systronix/ultim8x64/kicad/ultim8x64_pdf/ultim8x64.pdf

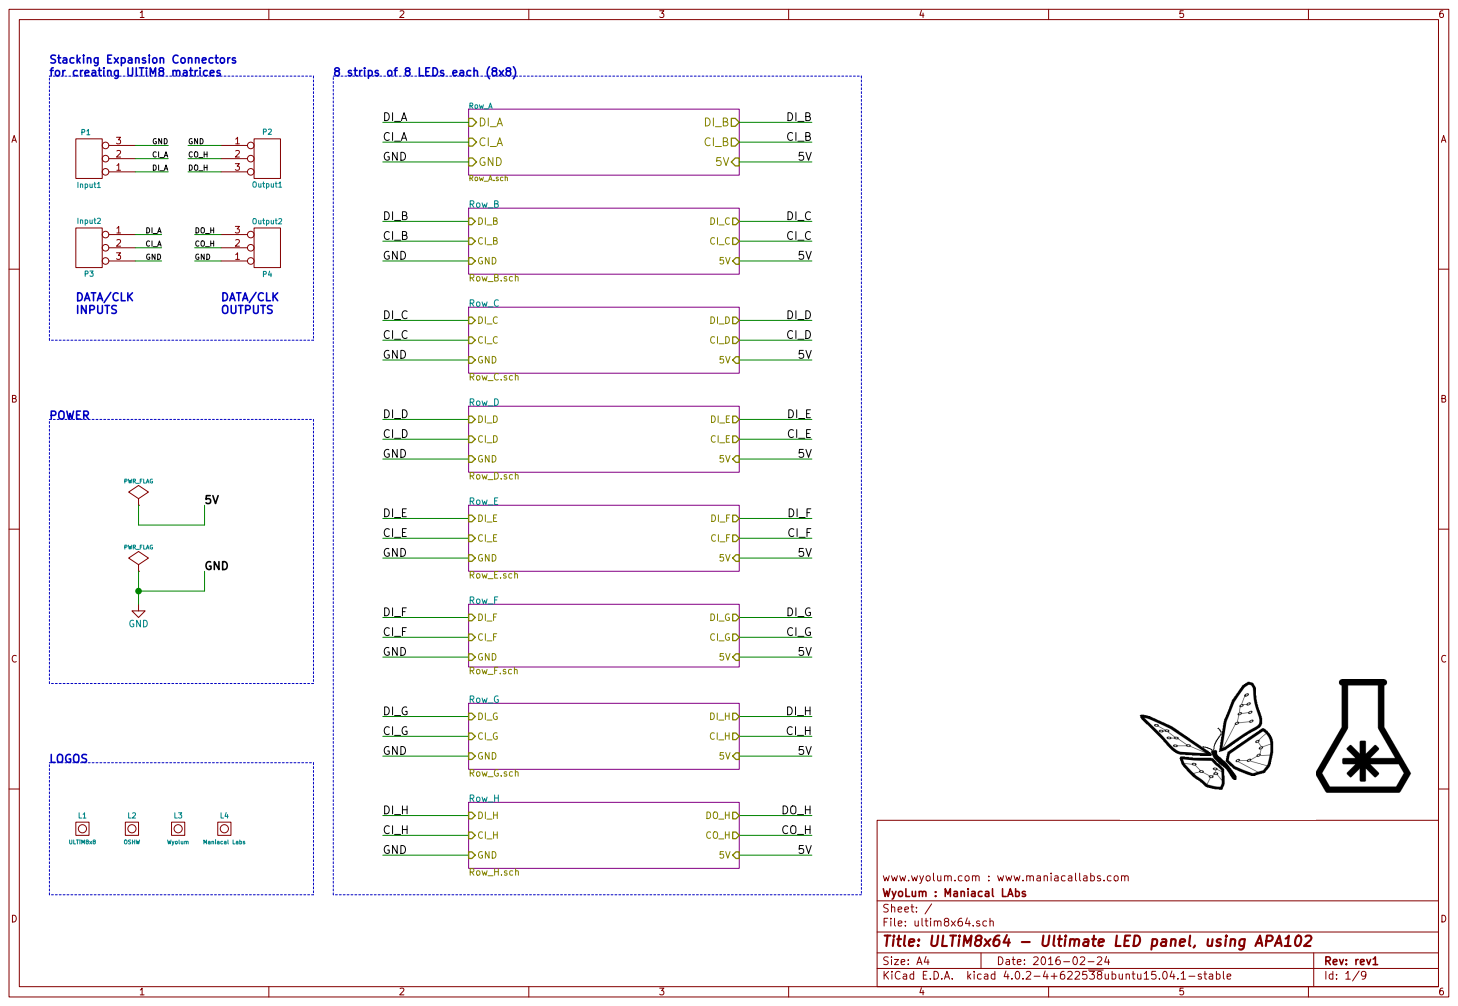
[picture p13: page 1]

8 strips of 8 LEDs each (8x8)

www.wyolum.com : www.maniacallabs.com
File: ultim8x64.sch Sheet: / WyoLum : Maniacal LAbs

Id: 1/9 Title: ULTiM8x64 - Ultimate LED panel, using APA102

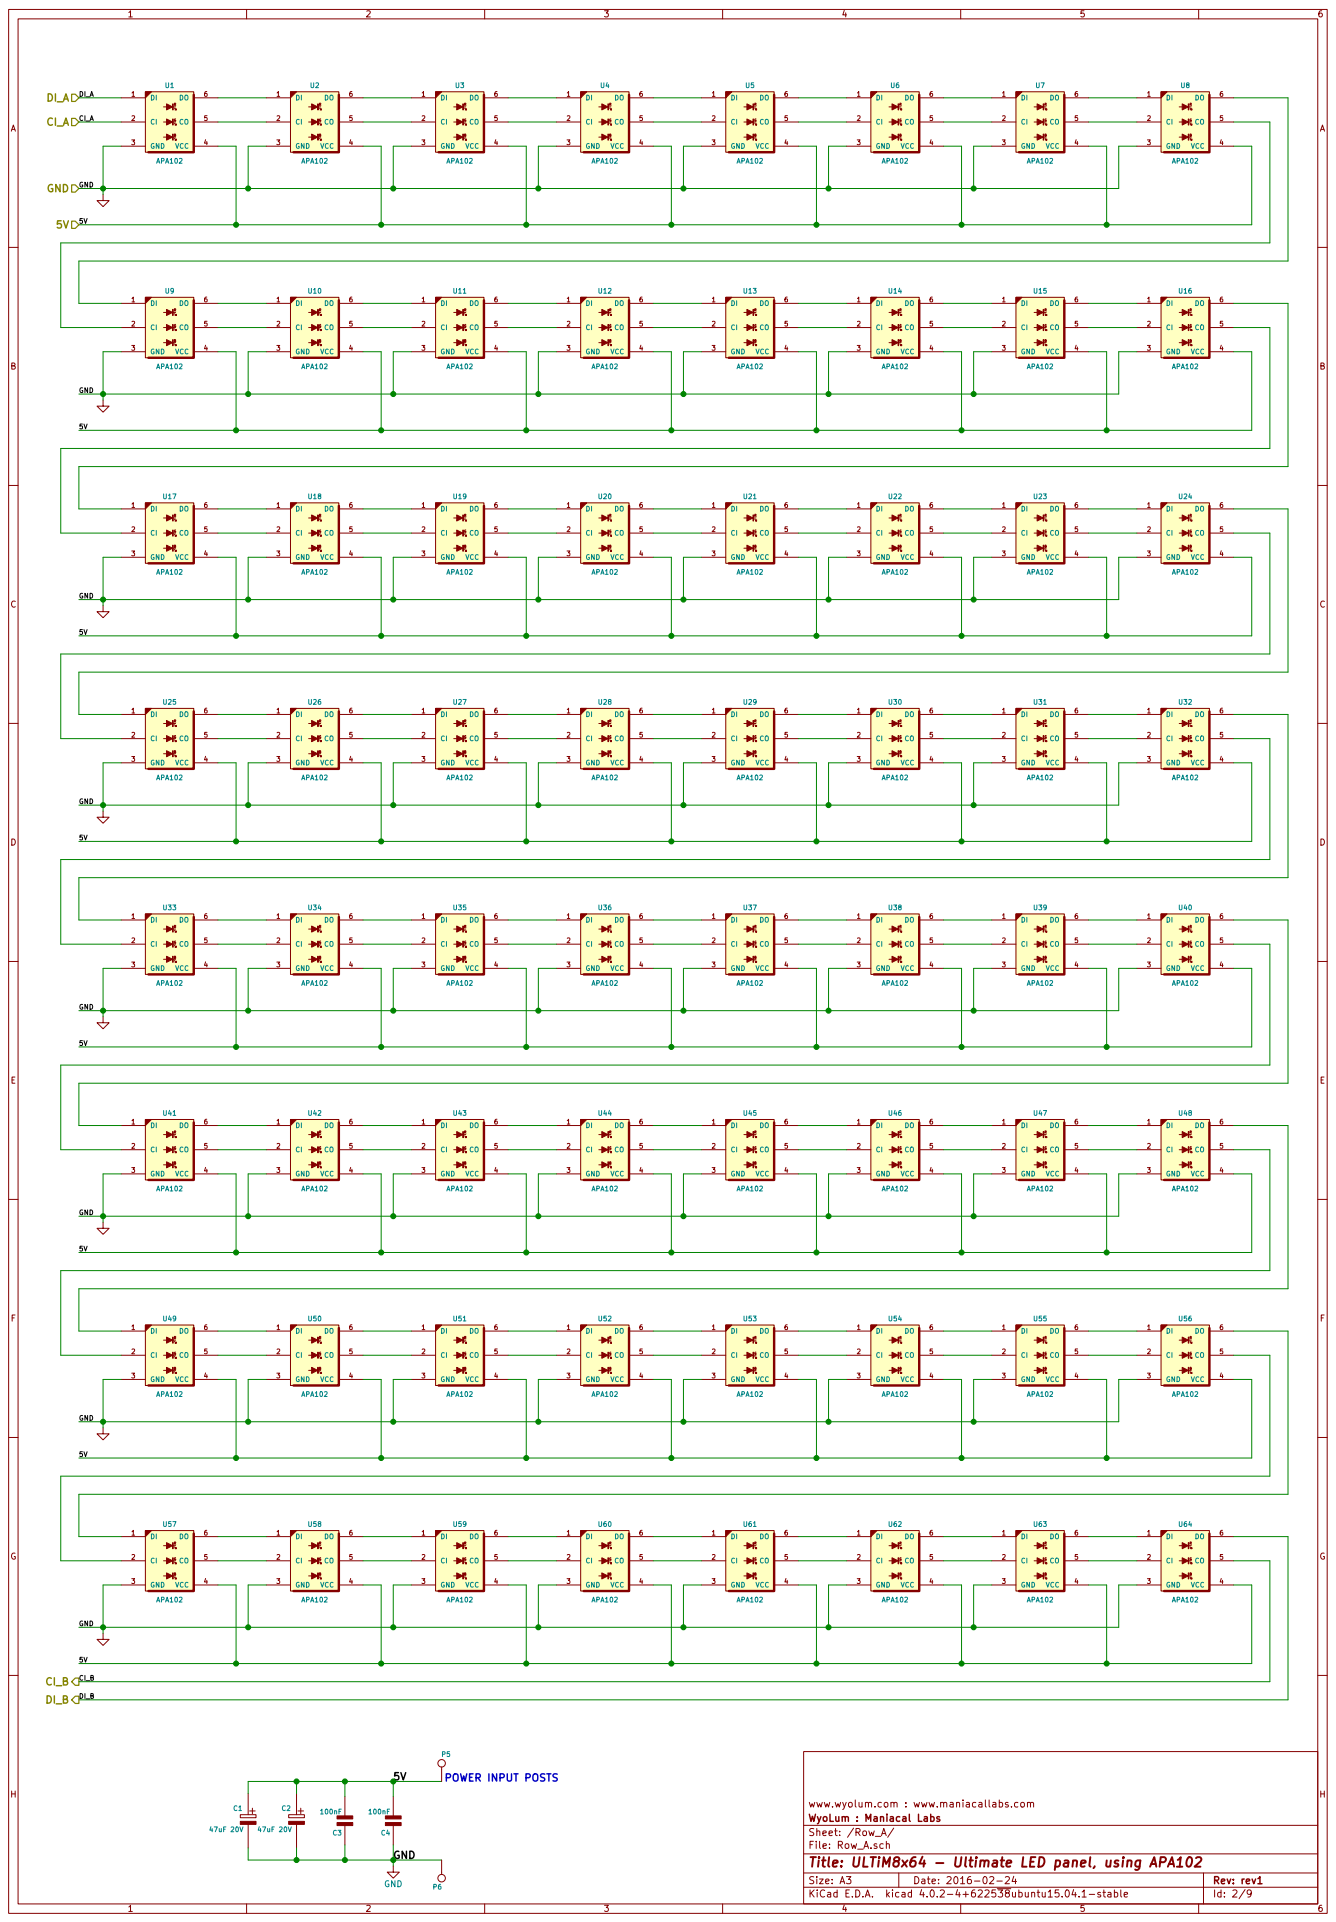
[picture p14: page 2]

www.wyolum.com : www.maniacallabs.com
WyoLum : Maniacal Labs
Sheet: /Row_A/
File: Row_A.sch
Id: 2/9 Title: ULTiM8x64 - Ultimate LED panel, using APA102

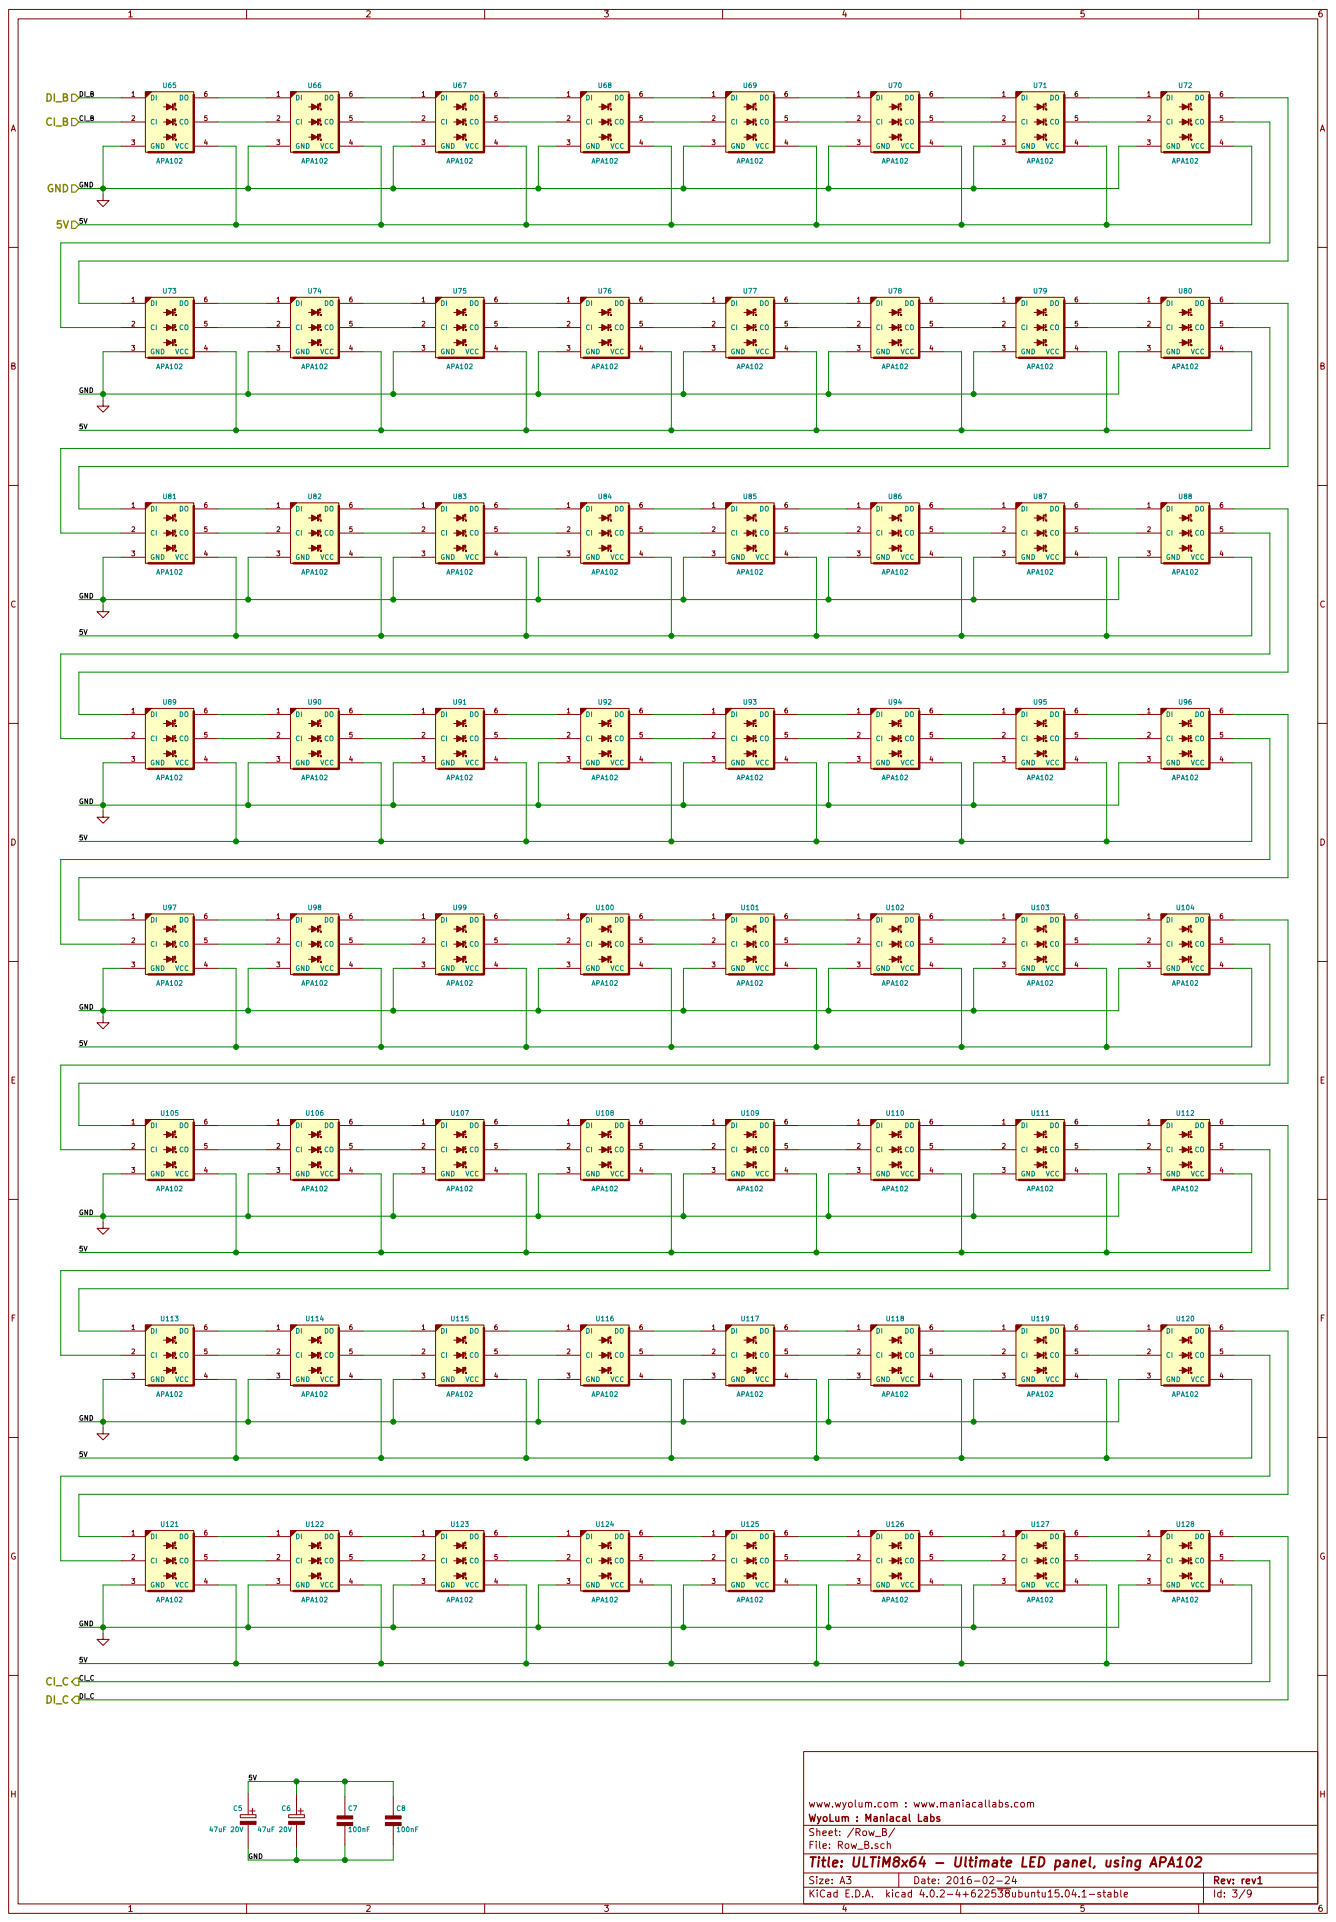
[picture p15: page 3]

Sheet: /Row_B/
File: Row_B.sch
Id: 3/9 Title: ULTiM8x64 - Ultimate LED panel, using APA102

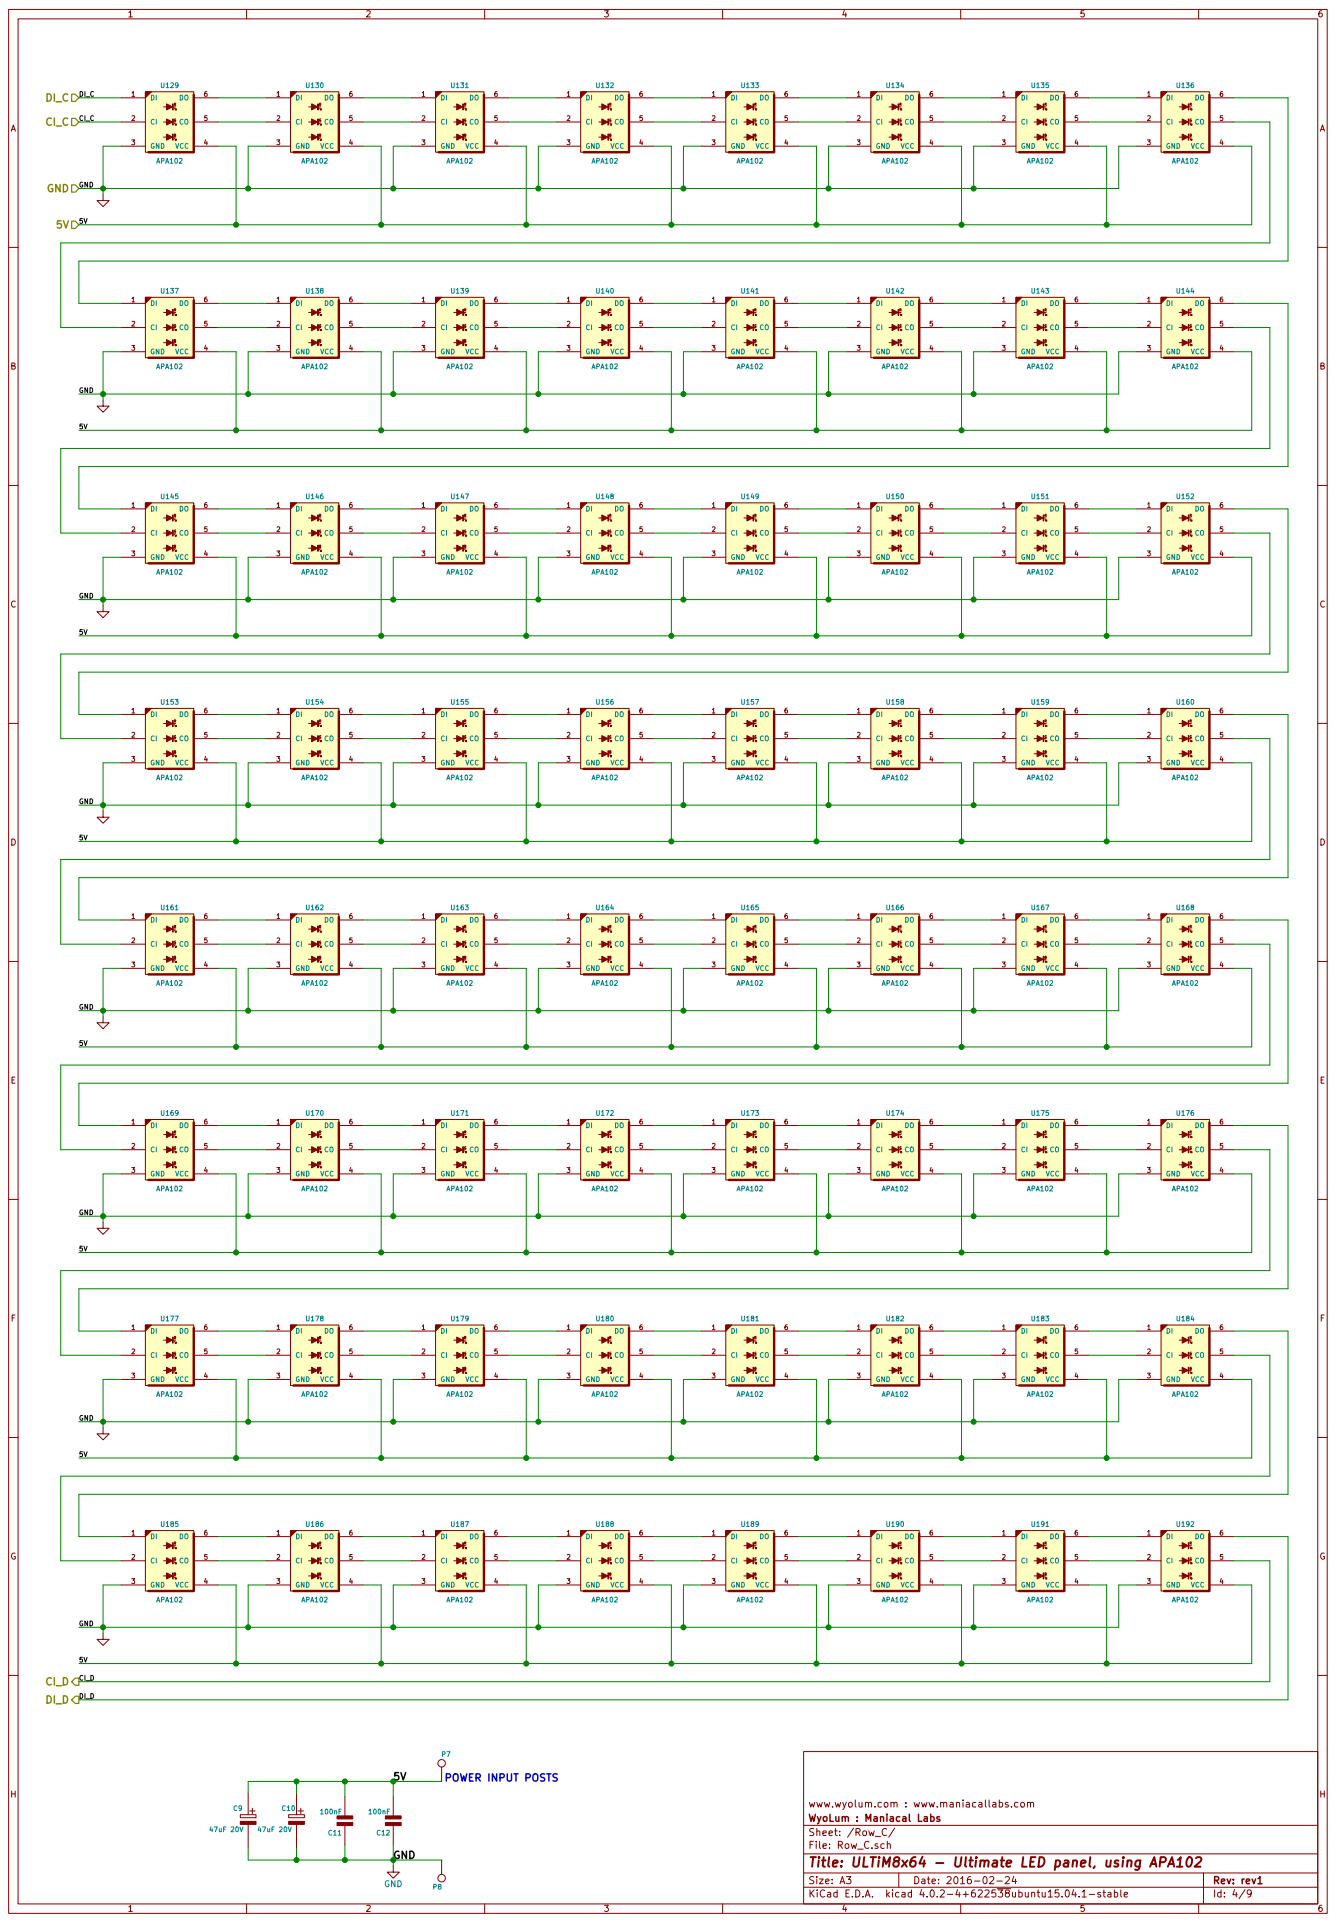
[picture p16: page 4]

Sheet: /Row_C/
File: Row_C.sch
Id: 4/9 Title: ULTiM8x64 - Ultimate LED panel, using APA102

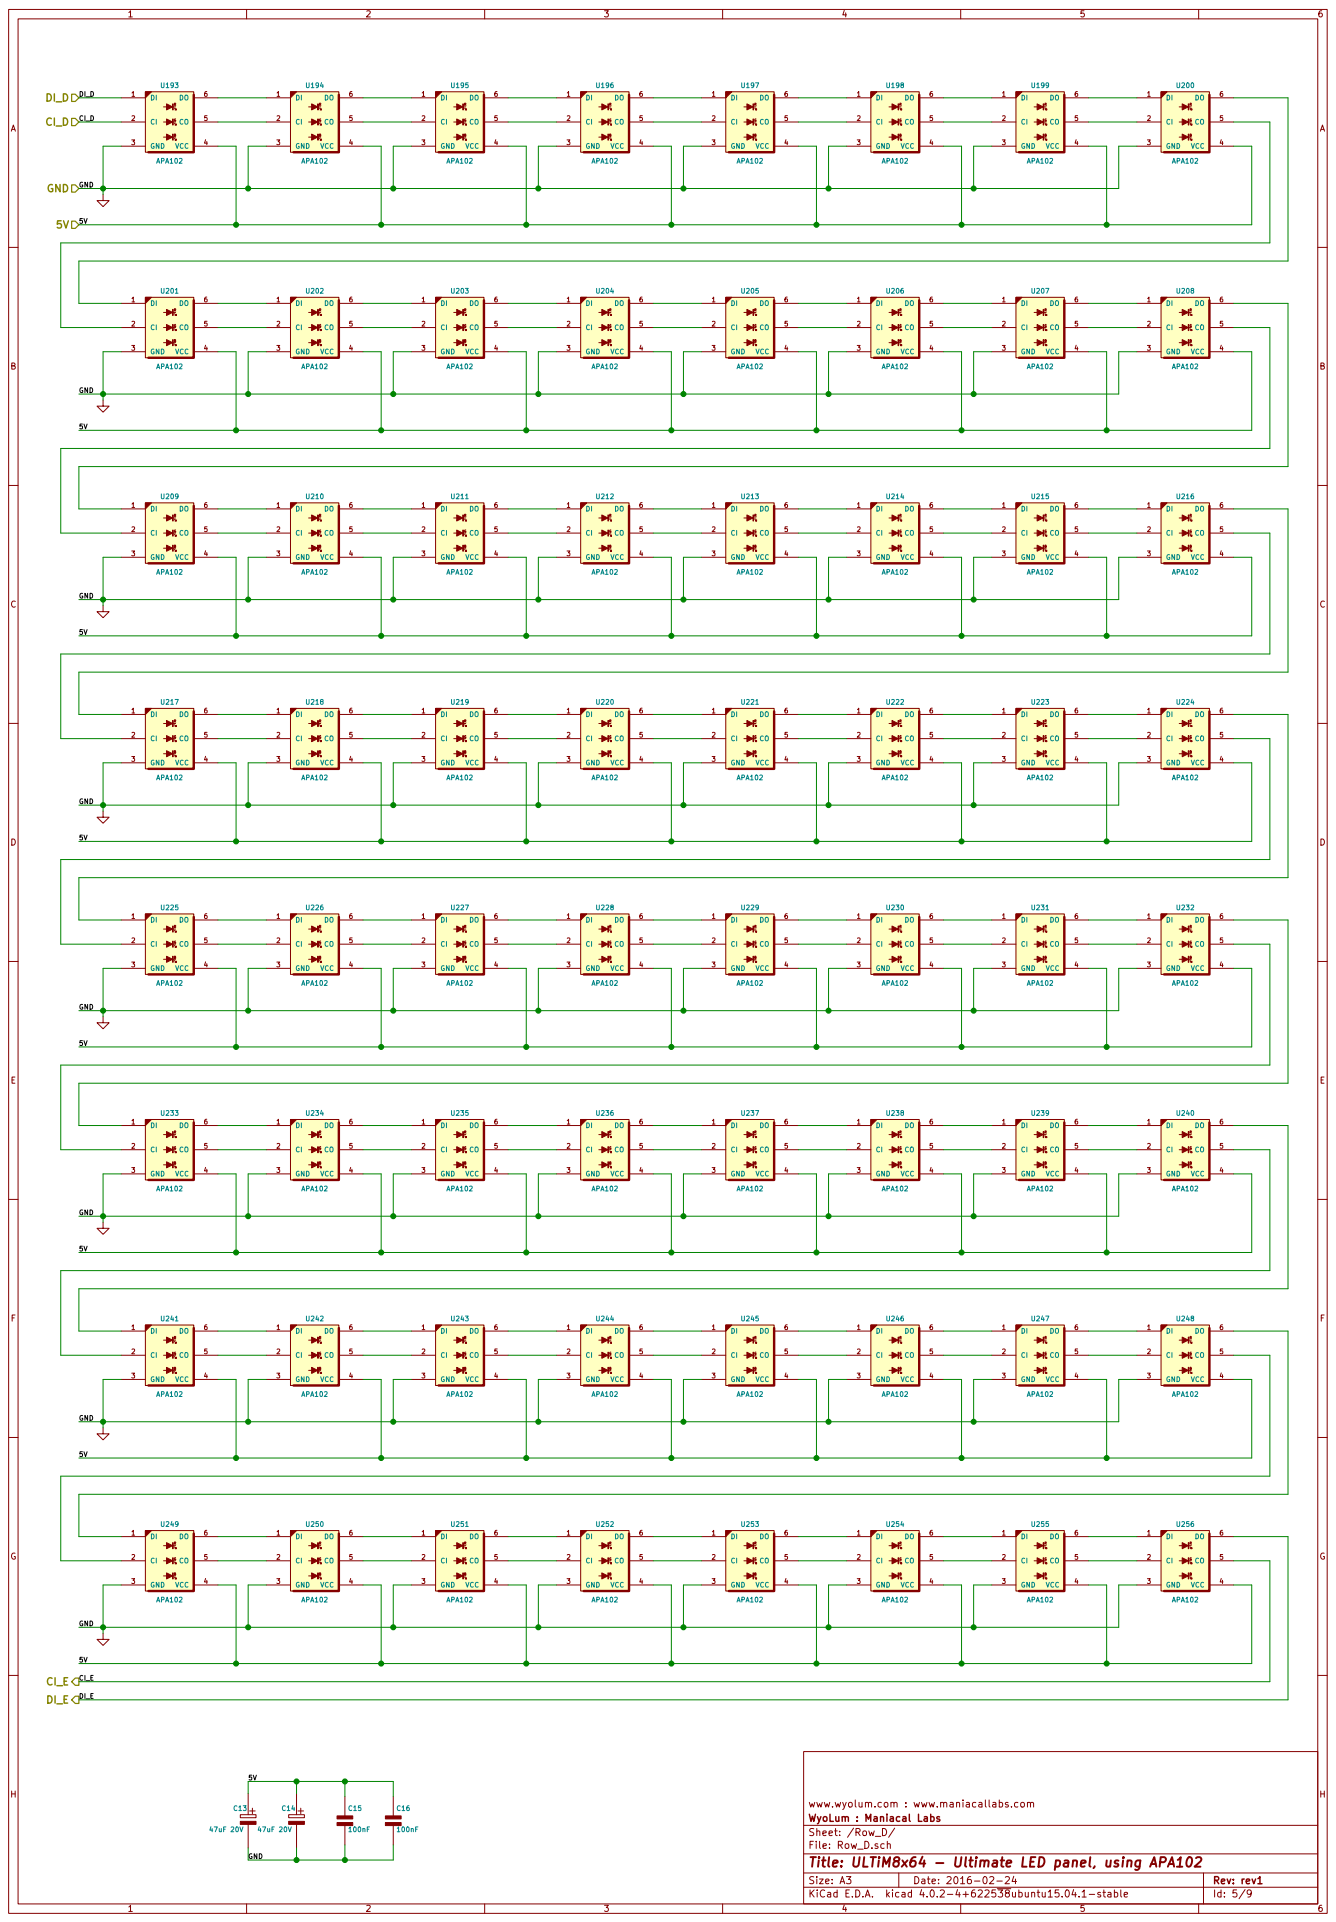
[picture p17: page 5]

Sheet: /Row_D/
File: Row_D.sch
Id: 5/9 Title: ULTiM8x64 - Ultimate LED panel, using APA102

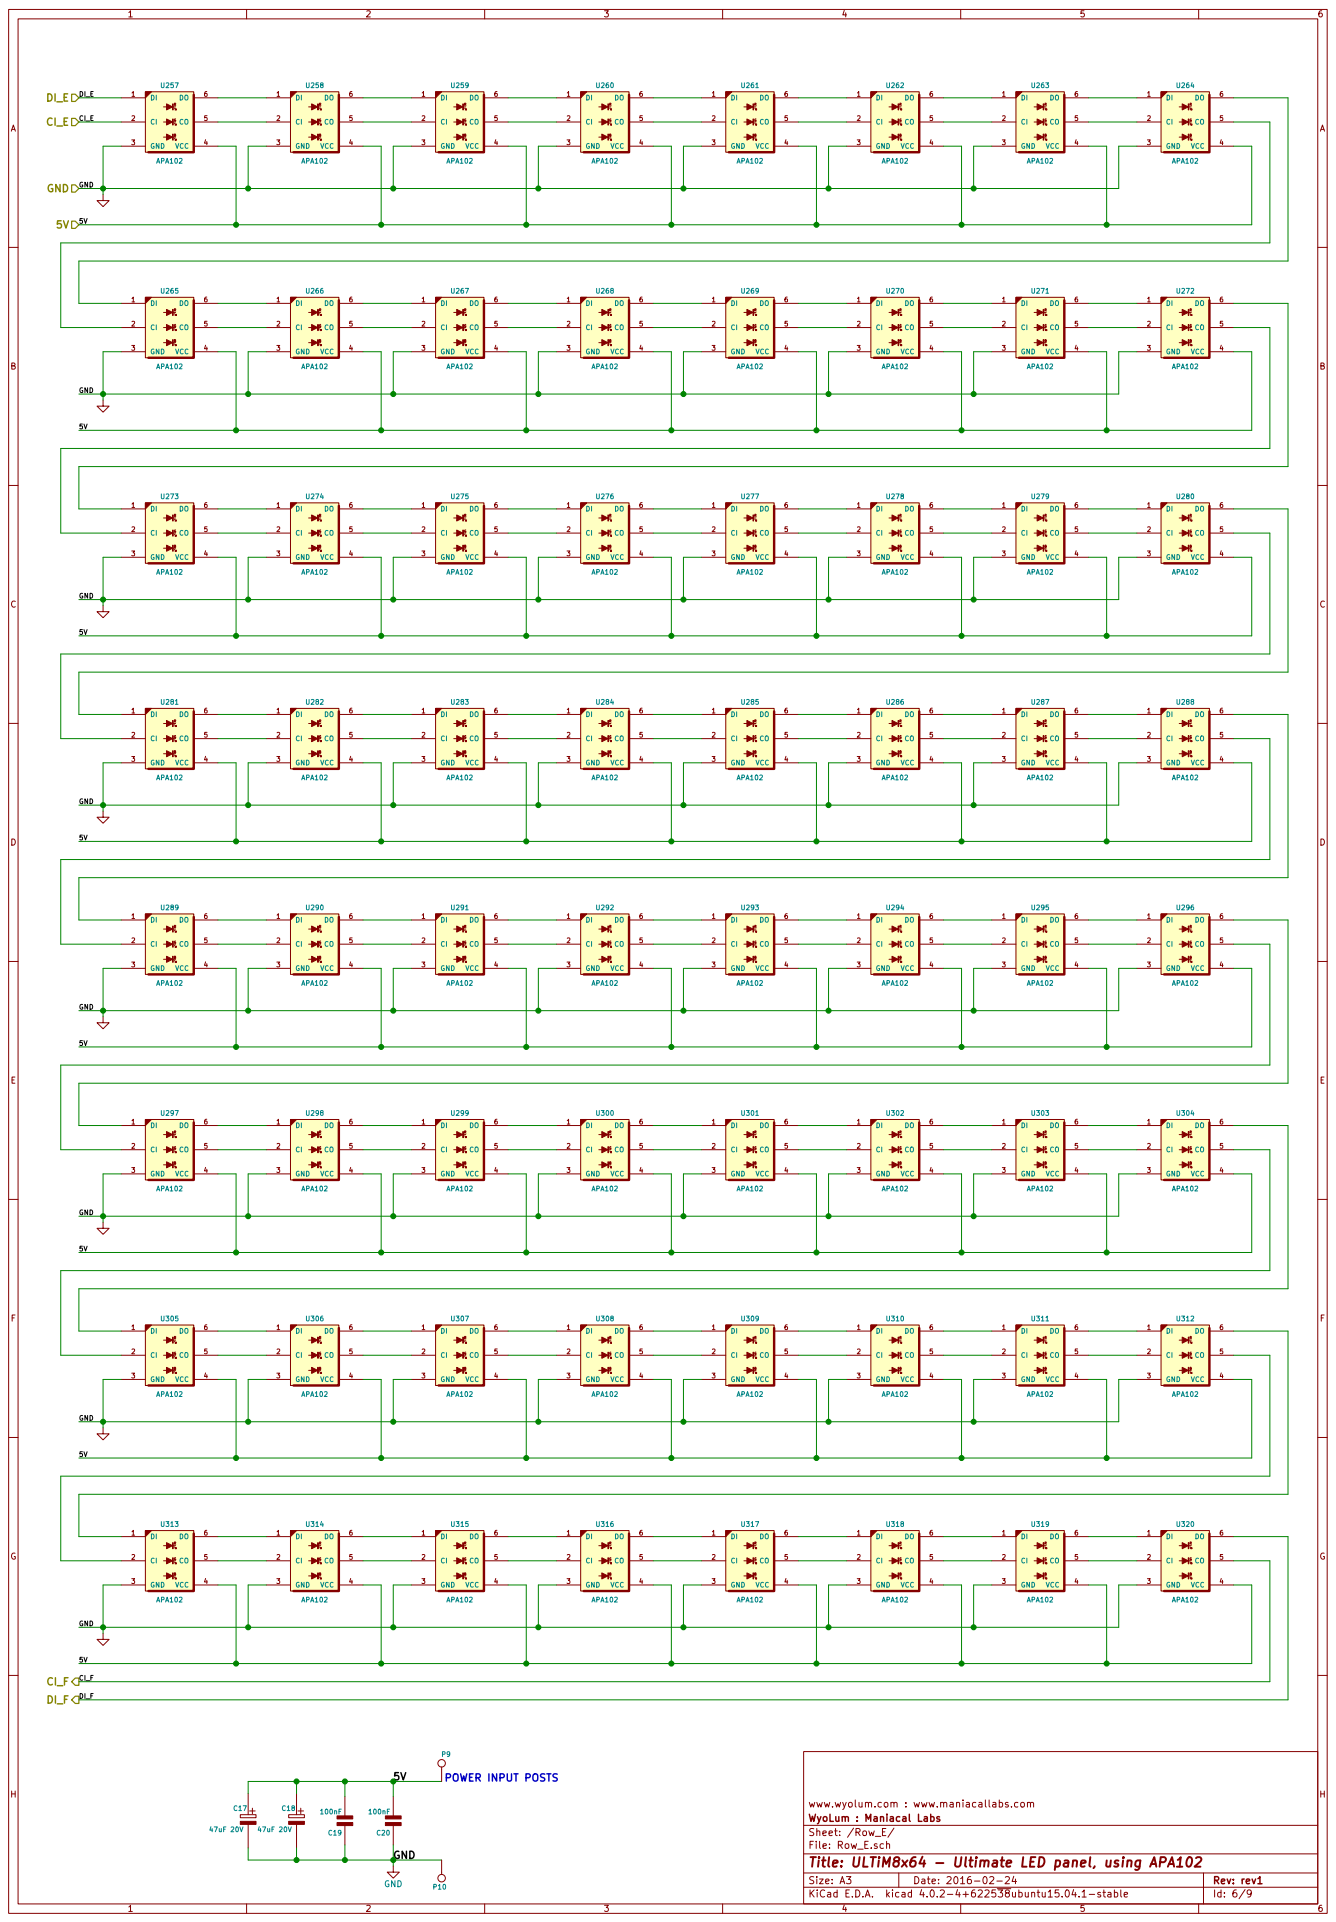
[picture p18: page 6]

Sheet: /Row_E/
File: Row_E.sch
Id: 6/9 Title: ULTiM8x64 - Ultimate LED panel, using APA102

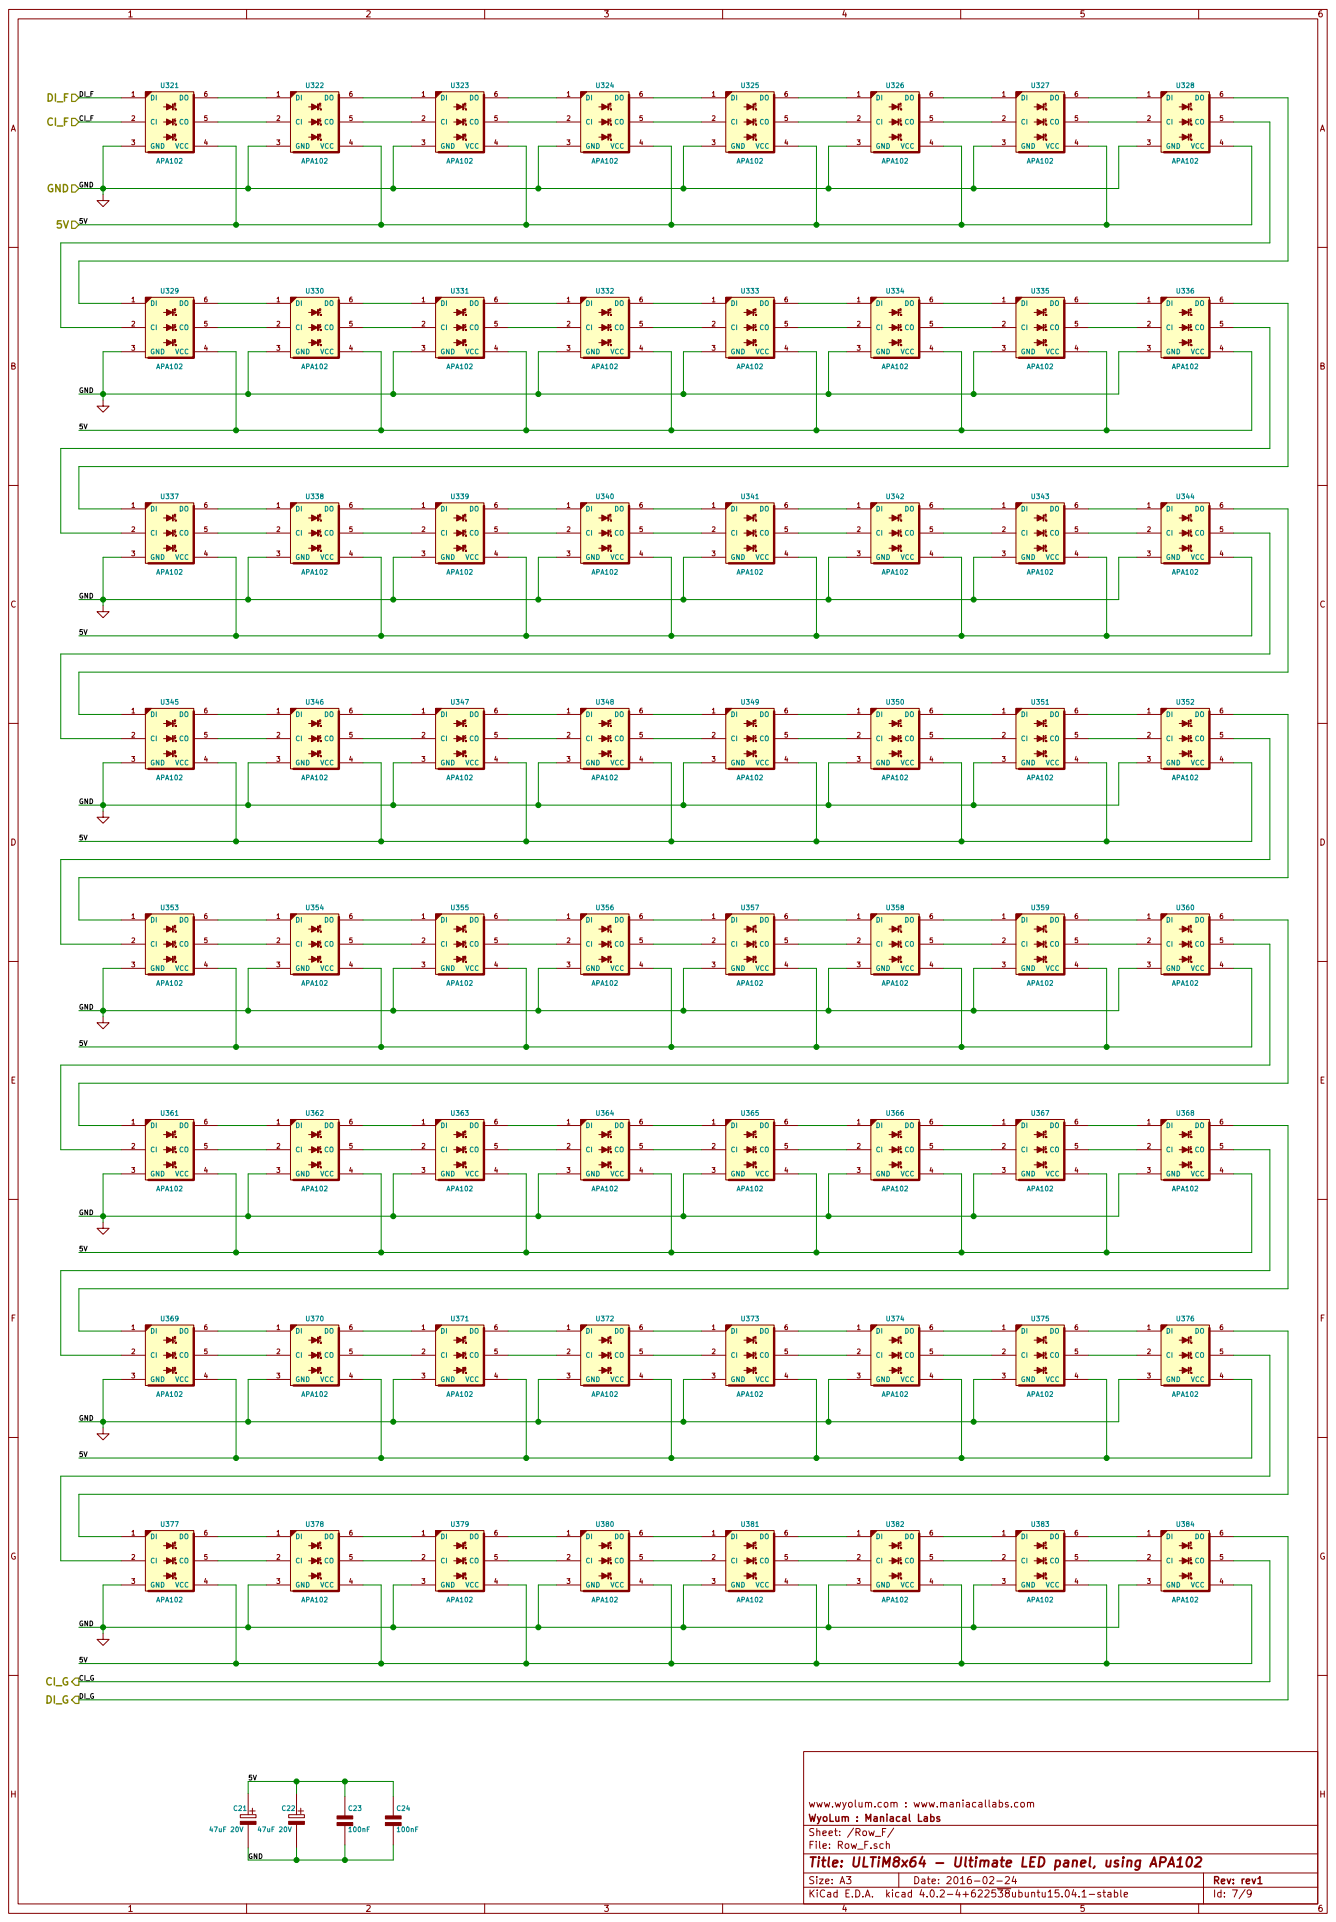
[picture p19: page 7]

Sheet: /Row_F/
File: Row_F.sch
Id: 7/9 Title: ULTiM8x64 - Ultimate LED panel, using APA102

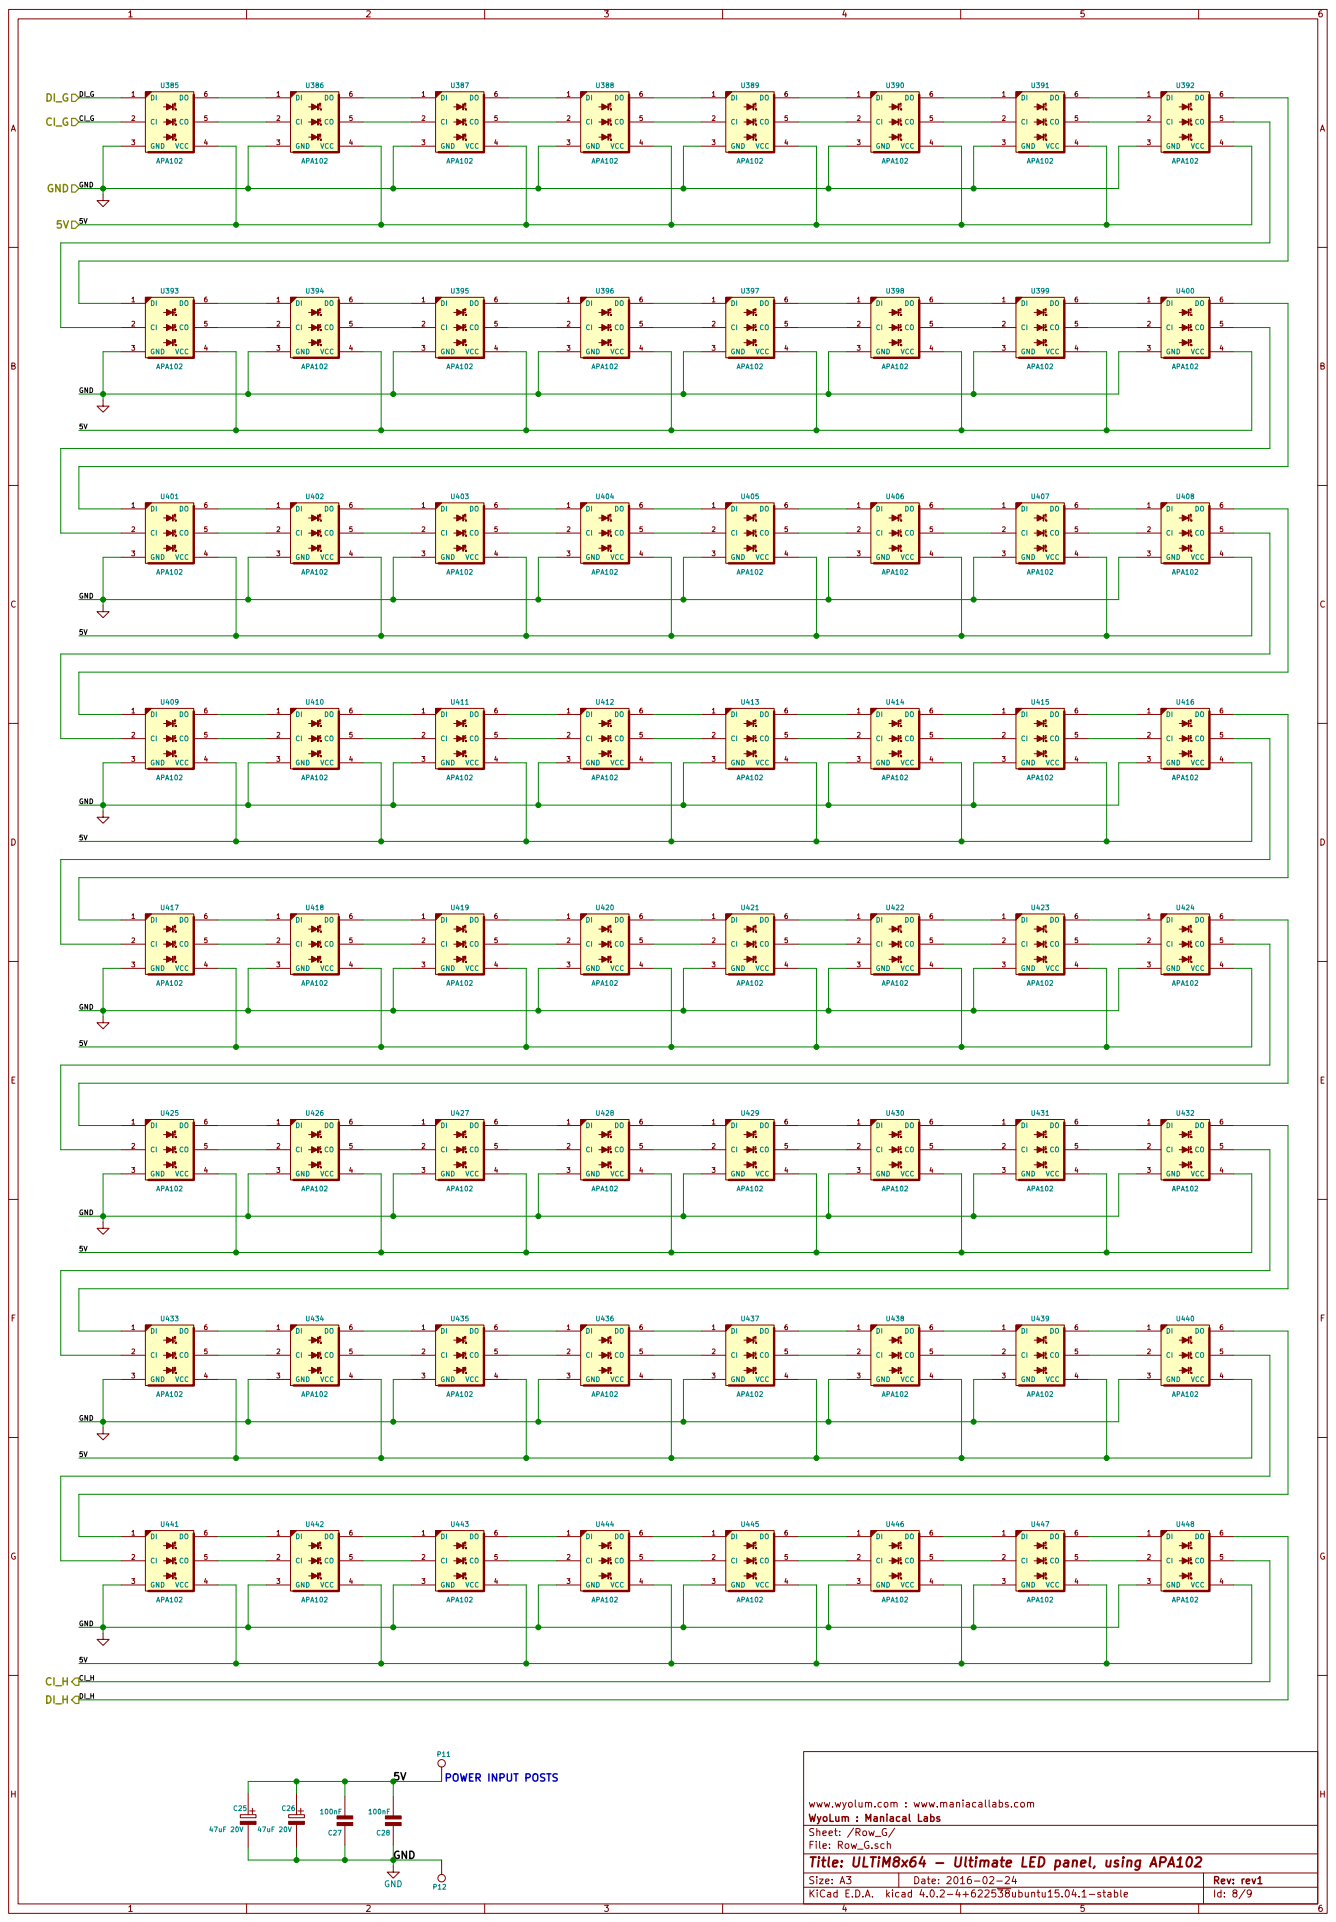
[picture p20: page 8]

Sheet: /Row_G/
File: Row_G.sch
Id: 8/9 Title: ULTiM8x64 - Ultimate LED panel, using APA102

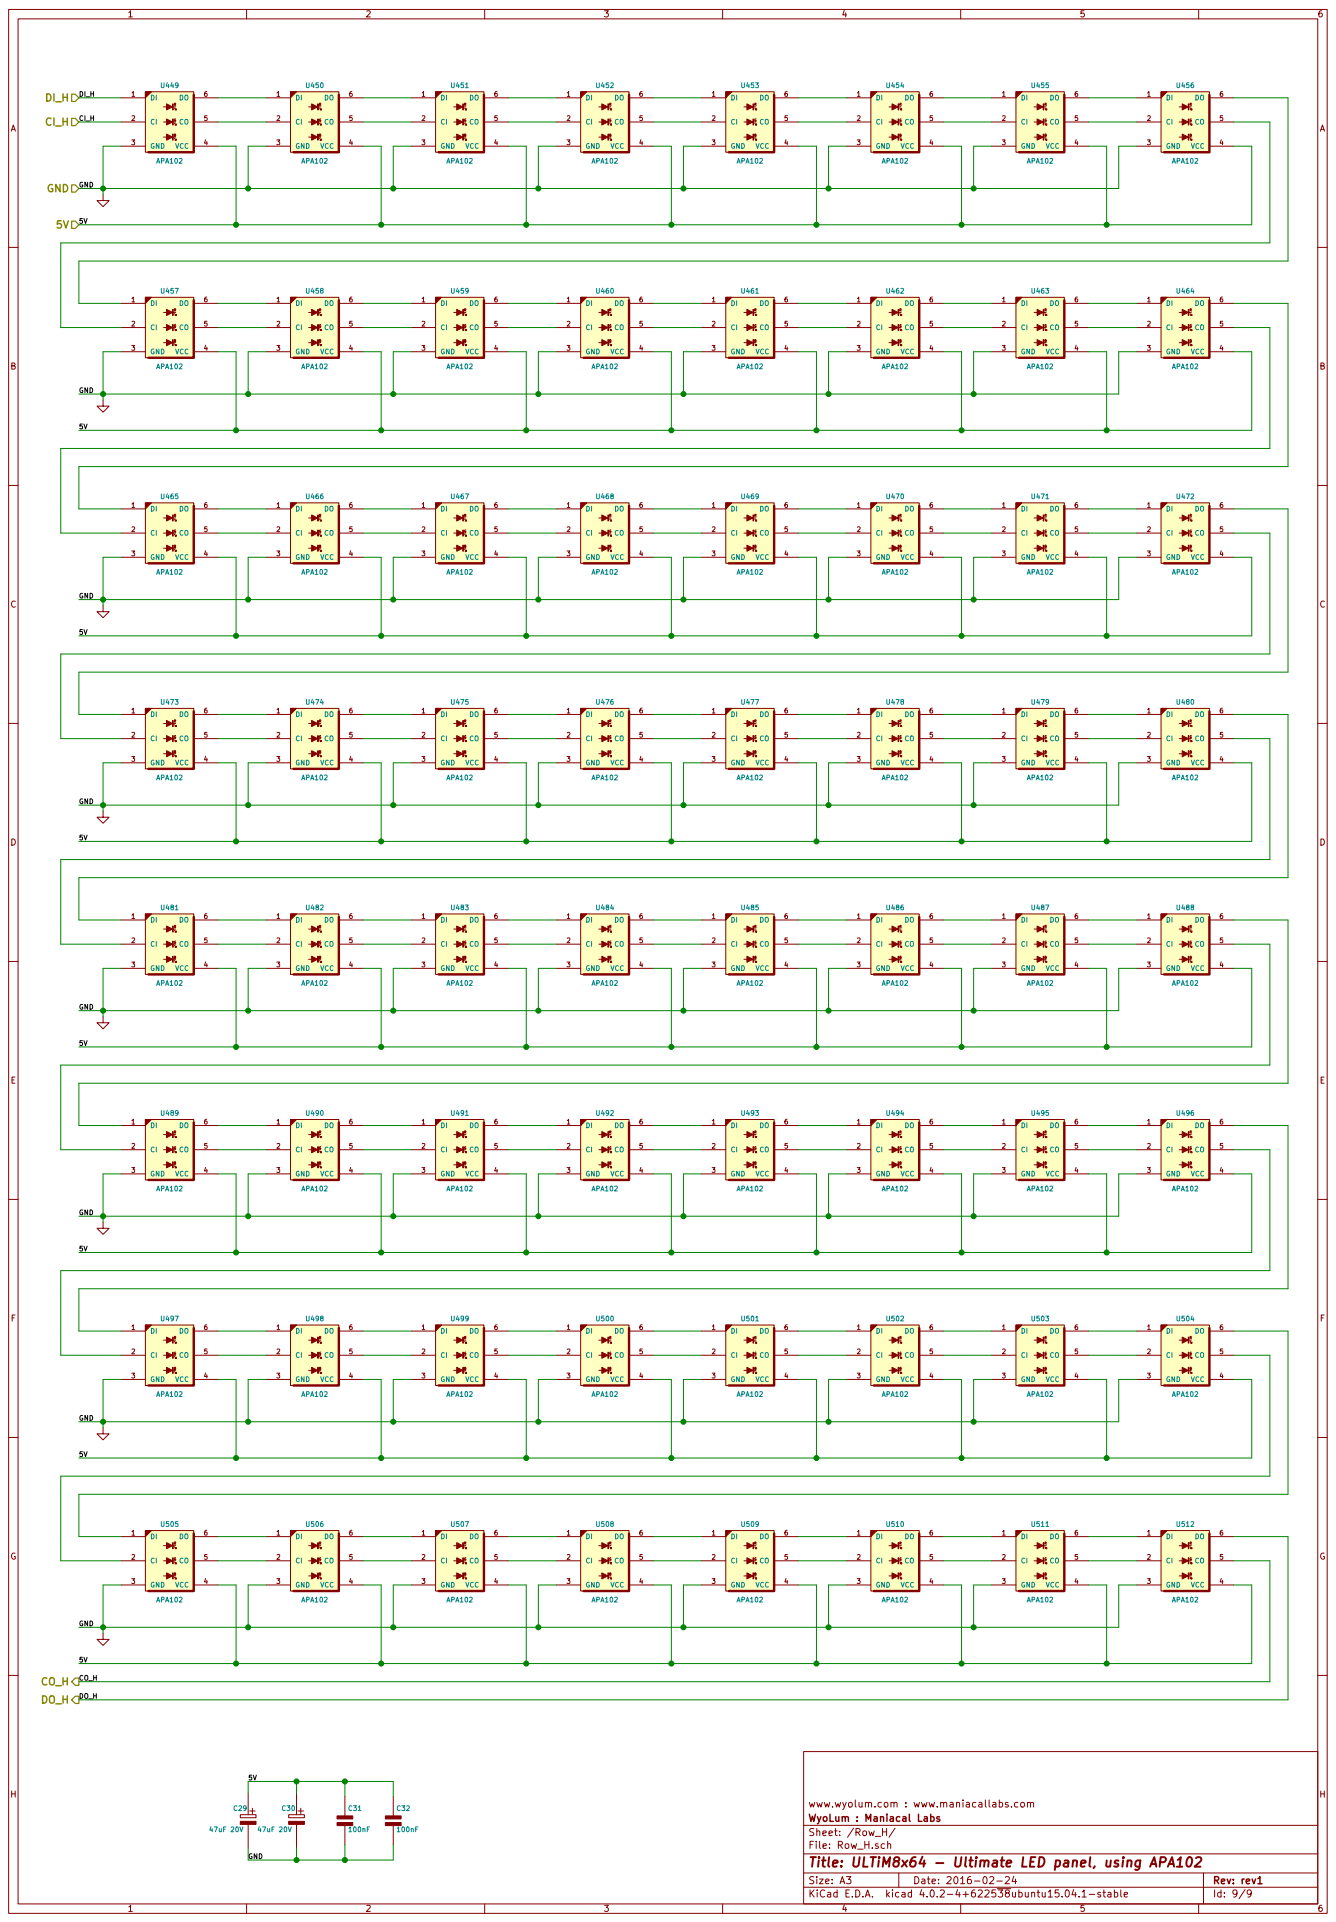
[picture p21: page 9]

Sheet: /Row_H/
File: Row_H.sch
Id: 9/9 Title: ULTiM8x64 - Ultimate LED panel, using APA102
